Sylkaron/Sylkaboard58/Layout__definition/bcase.dxf

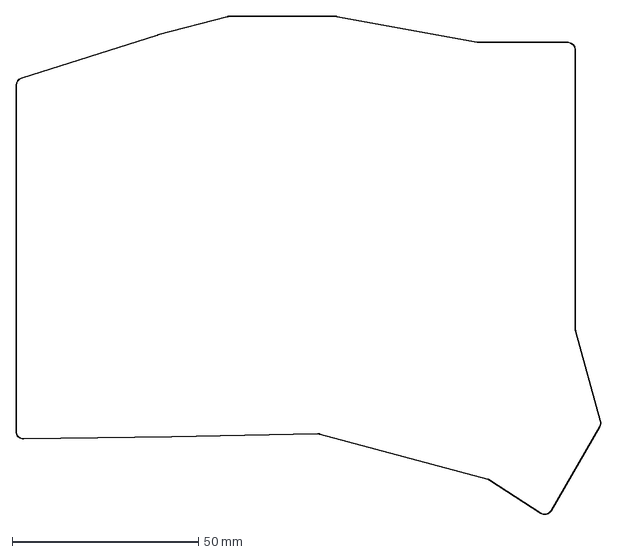
[picture p17: CAD file, 2026-09-22]
Layout__definition/bcase.dxf
157.1 x 133.8 mm
