Sylkaron/Sylkaboard58/Layout__definition/screen_hole.dxf

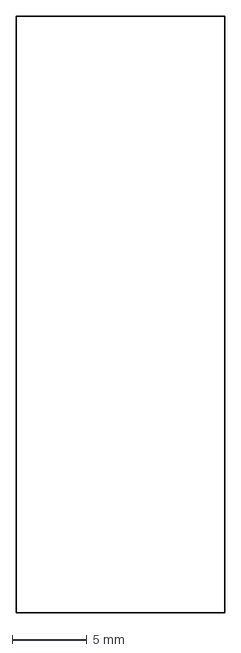
[picture p18: CAD file, 2026-09-22]
Layout__definition/screen_hole.dxf
14.0 x 40.0 mm
