Sylkaron/Sylkaboard58/Layout__definition/plboard.dxf

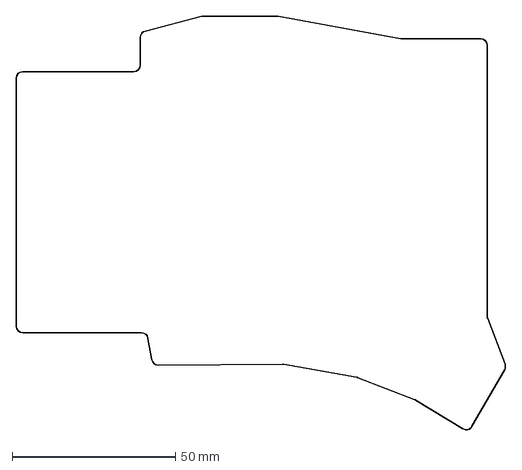
[picture p19: CAD file, 2026-09-22]
Layout__definition/plboard.dxf
149.9 x 126.8 mm
