Sylkaron/Sylkaboard58/Layout__definition/screen_support.dxf

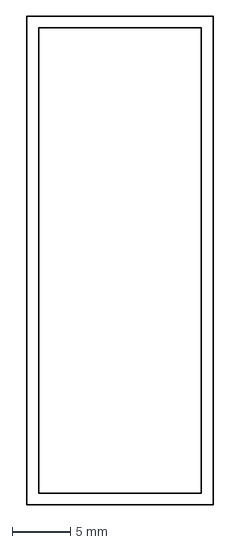
[picture p20: CAD file, 2026-09-22]
Layout__definition/screen_support.dxf
16.0 x 42.0 mm
