Sylkaron/Sylkaboard58/Layout__definition/screen_padding.dxf

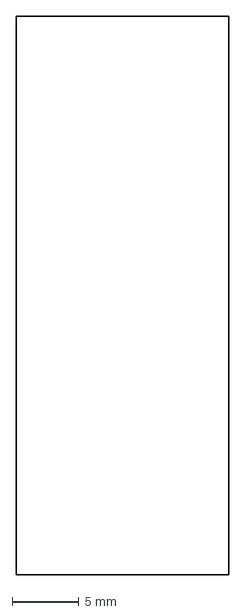
[picture p21: CAD file, 2026-09-22]
Layout__definition/screen_padding.dxf
16.0 x 42.0 mm
