Sylkaron/Sylkaboard58/Fabrications/SVG/Sylkaboard-B_Cu.png

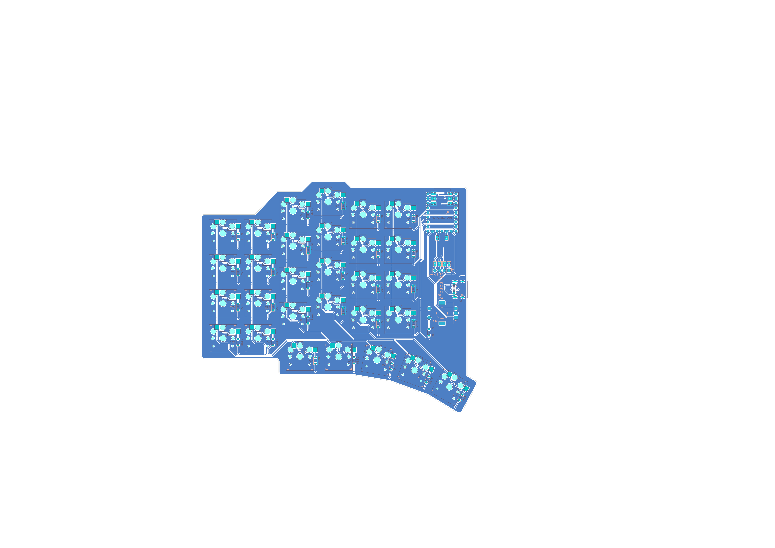
Fabrications/SVG/Sylkaboard-B_Cu.png
